nalithlakshan/FYP-MorATE/QT Software Project/img/bage_arrow.png

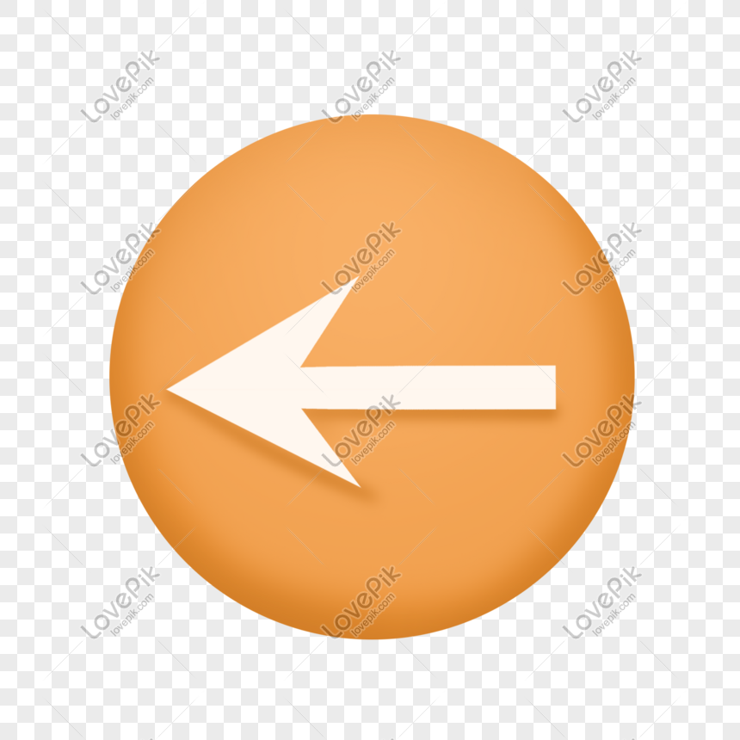
QT Software Project/img/bage_arrow.png
