nalithlakshan/FYP-MorATE/QT Software Project/img/blue_arrow.png

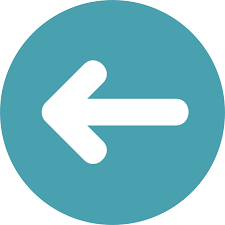
QT Software Project/img/blue_arrow.png
