nalithlakshan/FYP-MorATE/QT Software Project/img/failed_background.png

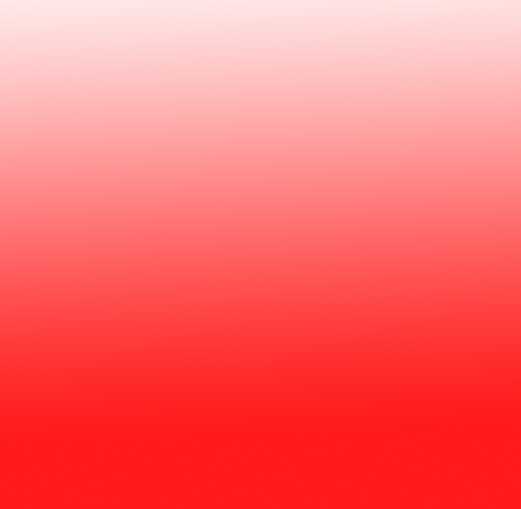
QT Software Project/img/failed_background.png
