nalithlakshan/FYP-MorATE/QT Software Project/img/IC2.png

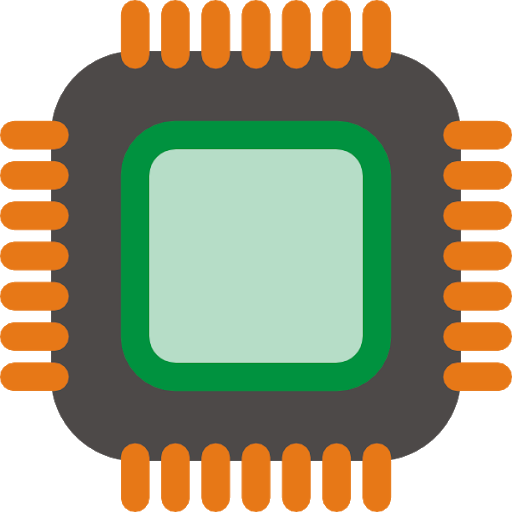
QT Software Project/img/IC2.png
