nalithlakshan/FYP-MorATE/QT Software Project/img/IC3.jpg

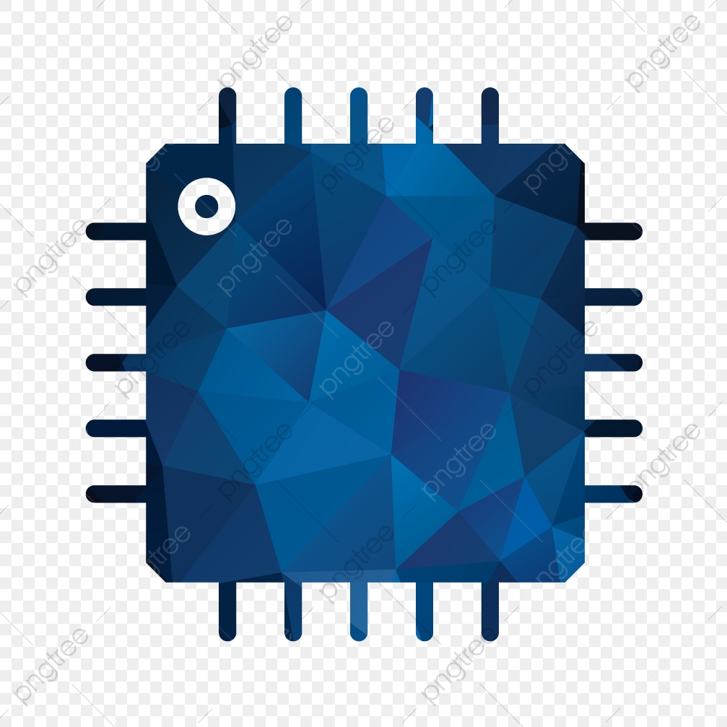
QT Software Project/img/IC3.jpg
