nalithlakshan/FYP-MorATE/QT Software Project/img/IC_grey.png

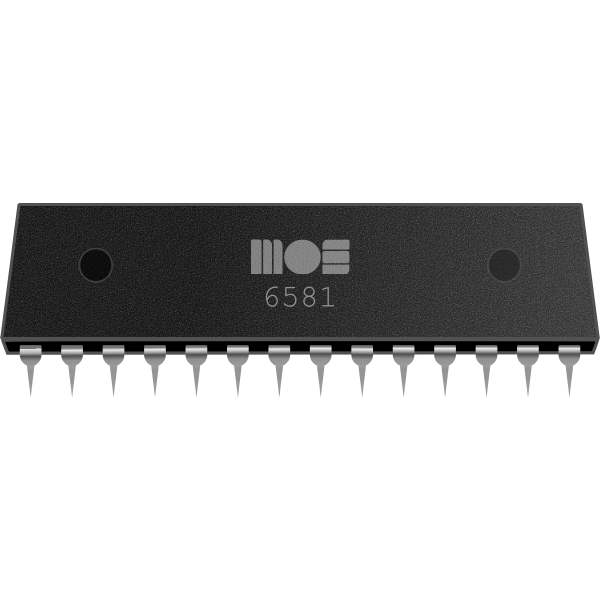
QT Software Project/img/IC_grey.png
