nalithlakshan/FYP-MorATE/QT Software Project/img/img_gear.png

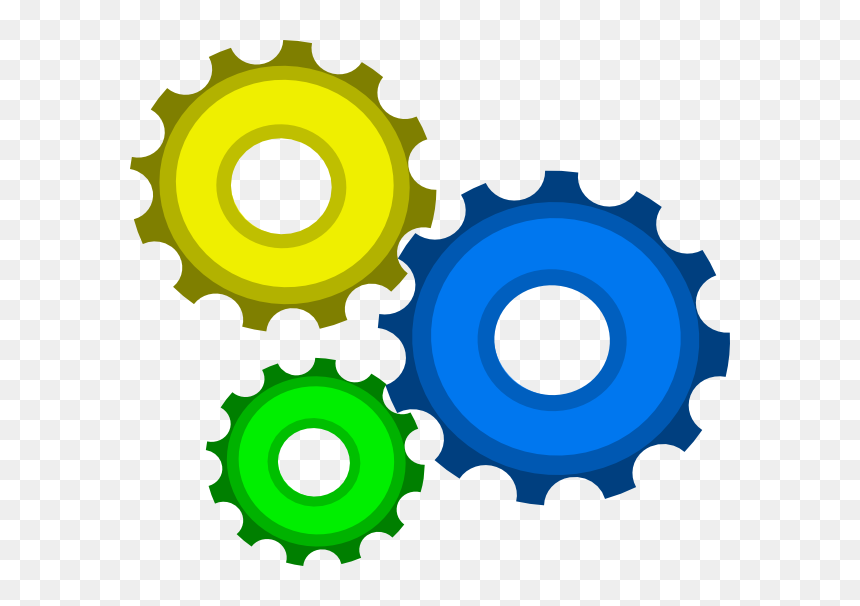
QT Software Project/img/img_gear.png
