nalithlakshan/FYP-MorATE/QT Software Project/img/yellow2.png

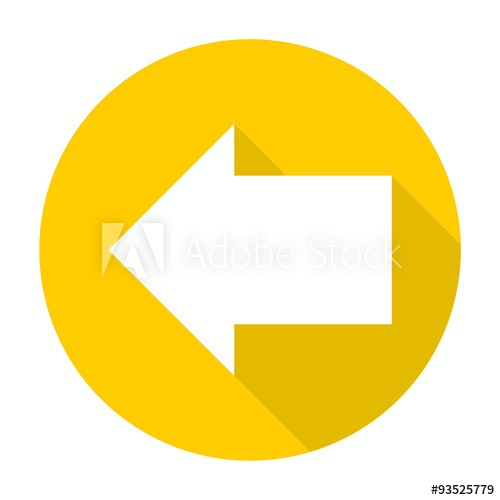
QT Software Project/img/yellow2.png
