nalithlakshan/FYP-MorATE/QT Software Project/img/testing_img2.jpg

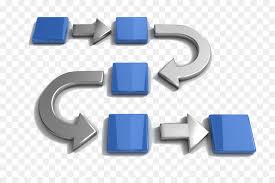
QT Software Project/img/testing_img2.jpg
