nalithlakshan/FYP-MorATE/QT Software Project/img/testing_img.jpg

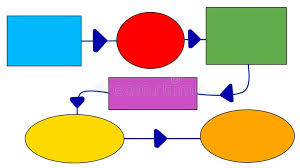
QT Software Project/img/testing_img.jpg
