nalithlakshan/FYP-MorATE/Firmware Projects/main_mcu/Core/Inc/si5351mcu.h

/*
 * si5351mcu - Si5351 library for Arduino MCU tuned for size and click-less
 *
 * Copyright (C) 2017 Pavel Milanes <pavelmc@gmail.com>
 *
 * Many chunk of codes are derived-from/copied from other libs
 * all GNU GPL licenced:
 *  - Linux Kernel (www.kernel.org)
 *  - Hans Summers libs and demo code (qrp-labs.com)
 *  - Etherkit (NT7S) Si5351 libs on github
 *  - DK7IH example.
 *  - Jerry Gaffke integer routines for the bitx20 group
 *
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
 * You should have received a copy of the GNU General Public License
 * along with this program.  If not, see <http://www.gnu.org/licenses/>.
 */


/****************************************************************************
 *  This lib tricks:
 *
 * CLK0 will use PLLA
 * CLK1 will use PLLB
 * CLK2 will use PLLB
 *
 * Lib defaults
 * - XTAL is 27 Mhz.
 * - Always put the internal 8pF across the xtal legs to GND
 * - lowest power output (2mA)
 * - After the init all outputs are off, you need to enable them in your code.
 *
 * The correction procedure is not for the PPM as other libs, this
 * is just +/- Hz to the XTAL freq, you may get a click noise after
 * applying a correction
 *
 * The init procedure is mandatory as it set the Xtal (the default or a custom
 * one) and prepare the Wire (I2C) library for operation.
 ****************************************************************************/

#ifndef SI5351MCU_H
#define SI5351MCU_H

// rigor includes

#include "i2c.h"

// default I2C address of the Si5351
#define SIADDR 0x60

// register's power modifiers
#define SIOUT_2mA 0
#define SIOUT_4mA 1
#define SIOUT_6mA 2
#define SIOUT_8mA 3

// registers base (2mA by default)
#define SICLK0_R   76       // 0b1001100
#define SICLK12_R 108       // 0b1101100


class Si5351mcu {
    public:
        // default init procedure
        void init(void);

        // custom init procedure (XTAL in Hz);
        void init(uint32_t);

        // reset all PLLs
        void reset(void);

        // set CLKx(0..2) to freq (Hz)
        void setFreq(uint8_t, uint32_t);

        // pass a correction factor
        void correction(int32_t);

        // enable some CLKx output
        void enable(uint8_t);

        // disable some CLKx output
        void disable(uint8_t);

        // disable all outputs
        void off(void);

        // set power output to a specific clk
        void setPower(uint8_t, uint8_t);

        // var to check the clock state
        bool clkOn[3] = {0, 0, 0};


    private:
        // used to talk with the chip, via Arduino Wire lib
        void i2cWrite(uint8_t, uint8_t);

        // base xtal freq, over this we apply the correction factor
        // by default 27 MHz
        uint32_t base_xtal = 27000000L;

        // this is the work value, with the correction applied
        // via the correction() procedure
        uint32_t int_xtal = base_xtal;

        // clk# power holders (2ma by default)
        uint8_t clkpower[3] = {0, 0, 0};

        // local var to keep track of when to reset the "pll"
        /*********************************************************
         * BAD CONCEPT on the datasheet and AN:
         *
         * The chip has a soft-reset for PLL A & B but in
         * practice the PLL does not need to be reseted.
         *
         * Test shows that if you fix the Msynth output
         * dividers and move any of the VCO from bottom to top
         * the frequency moves smooth and clean, no reset needed
         *
         * The reset is needed when you changes the value of the
         * Msynth output divider, even so it's not always needed
         * so we use this var to keep track of all three and only
         * reset the "PLL" when this value changes to be sure
         *
         * It's a word (16 bit) because the final max value is 900
         *********************************************************/
        uint16_t omsynth[3] = {0, 0, 0};
};


#endif //SI5351MCU_H
